martinbros/9SegCounter/photos/frontOff.jpg

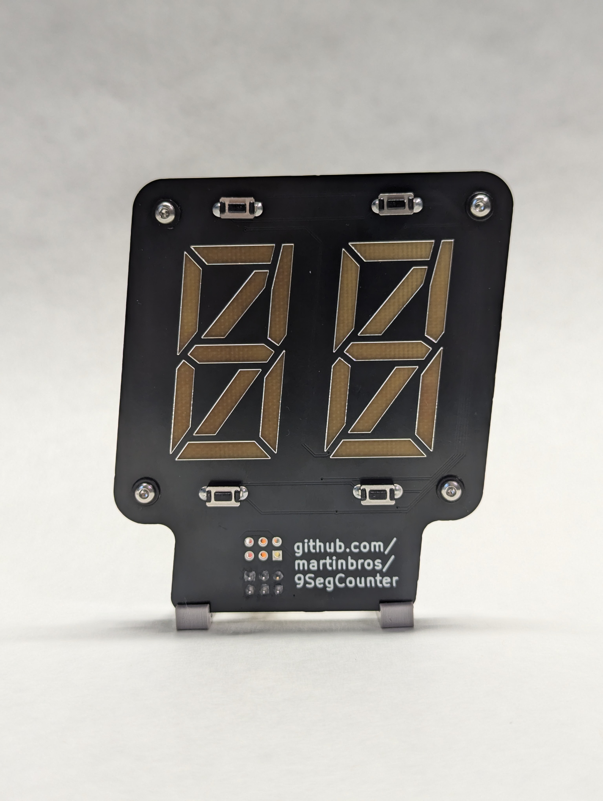
photos/frontOff.jpg
